snsten/Klein/docs/images/PCB.JPG

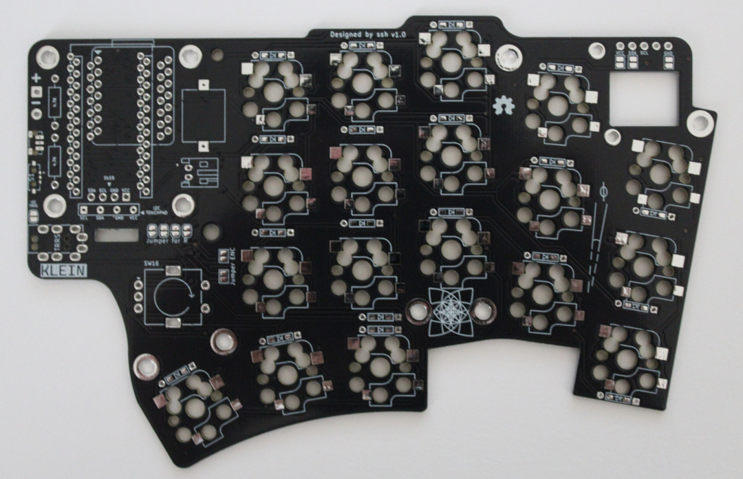
docs/images/PCB.JPG
