snsten/Klein/docs/images/buildguide/Buzzer.JPG

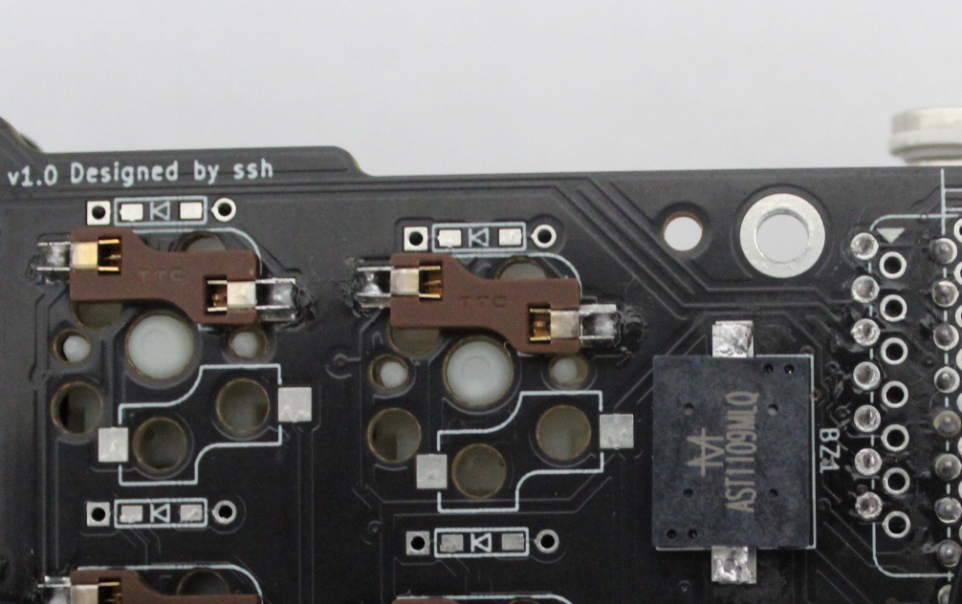
docs/images/buildguide/Buzzer.JPG
